abagher2/watch-calc-32/1mm_clearance_button.png

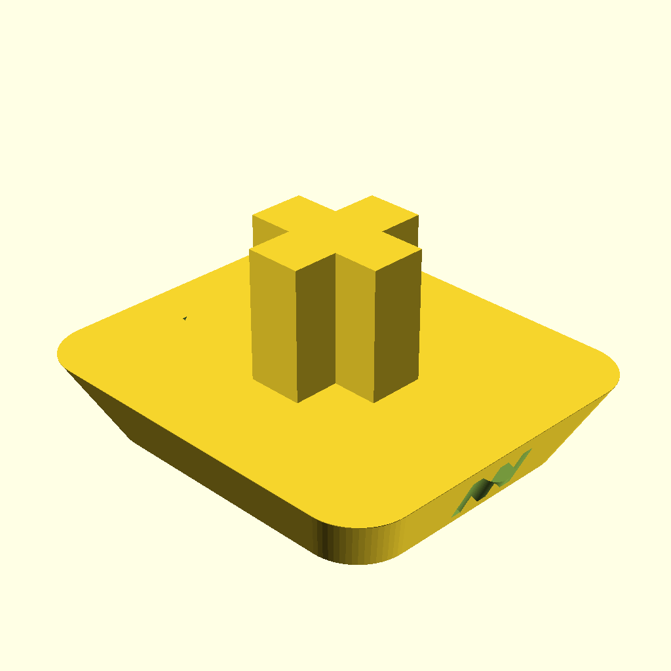
1mm_clearance_button.png
