abagher2/watch-calc-32/bridging_button.png

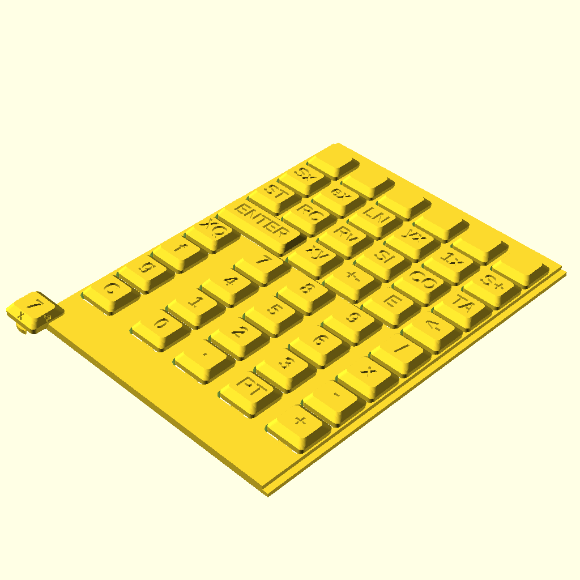
bridging_button.png
