abagher2/watch-calc-32/button_faceplate_captive.png

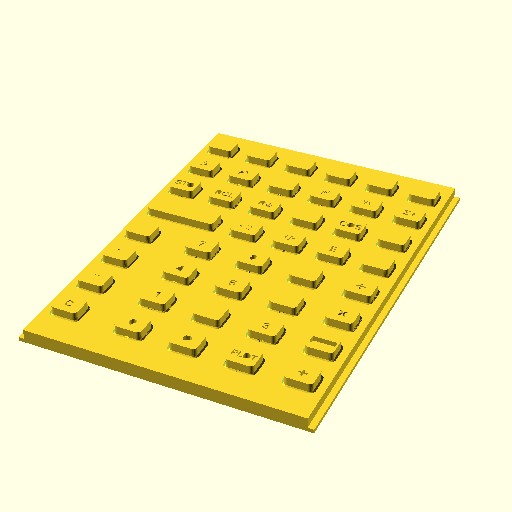
button_faceplate_captive.png
