abagher2/watch-calc-32/button_faceplate_captive_bottom.png

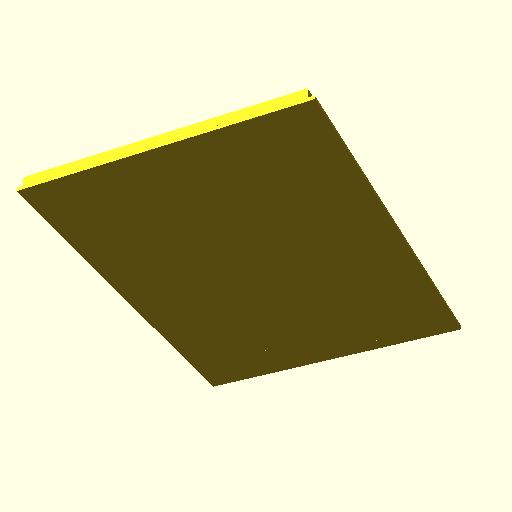
button_faceplate_captive_bottom.png
