abagher2/watch-calc-32/button_faceplate_fixed.png

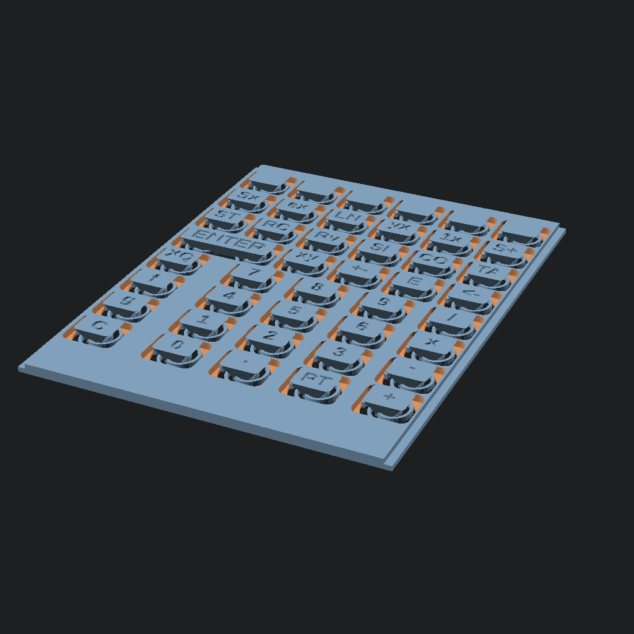
button_faceplate_fixed.png
