abagher2/watch-calc-32/button_faceplate_render4.png

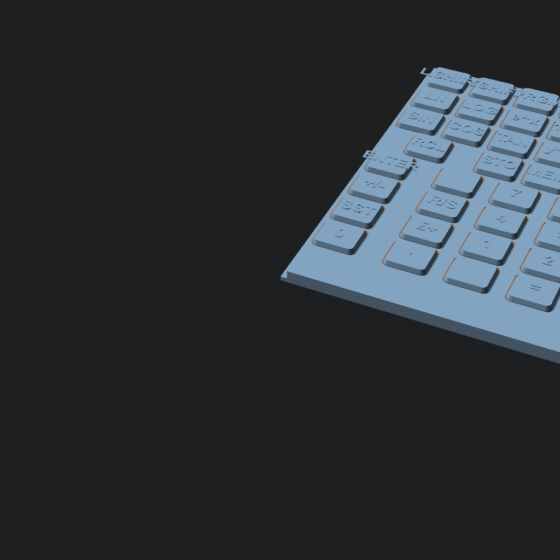
button_faceplate_render4.png
