abagher2/watch-calc-32/chiclet_emojis_updated.png

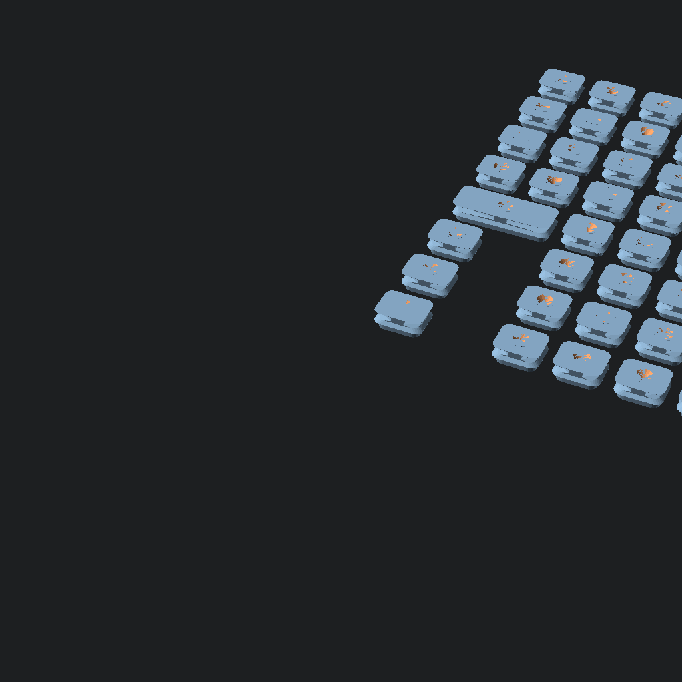
chiclet_emojis_updated.png
