abagher2/watch-calc-32/fastlane/screenshots_raw/en-US/iPad Pro 13-inch (M5)-1-Main.png

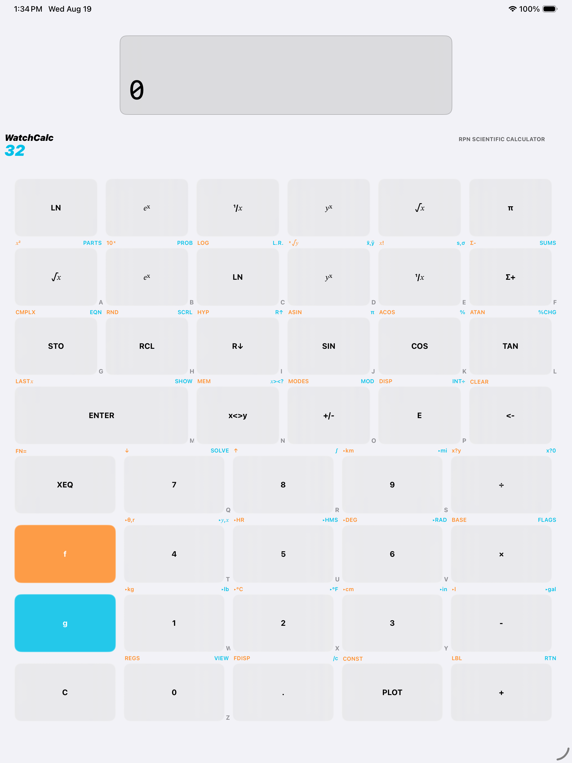
fastlane/screenshots_raw/en-US/iPad Pro 13-inch (M5)-1-Main.png
