abagher2/watch-calc-32/fastlane/screenshots_raw/en-US/iPad Pro 13-inch (M5)-2-Equation.png

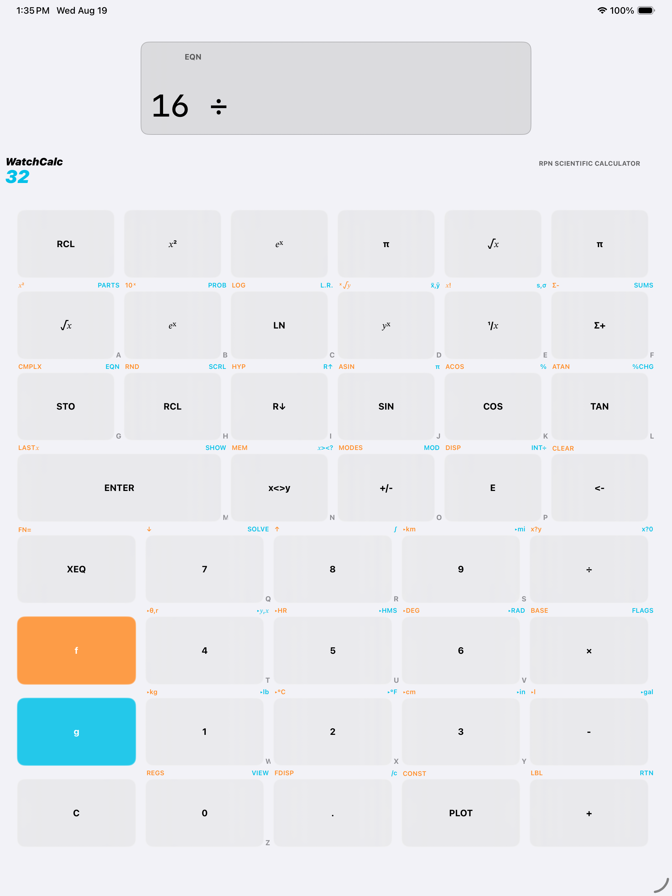
fastlane/screenshots_raw/en-US/iPad Pro 13-inch (M5)-2-Equation.png
