abagher2/watch-calc-32/fastlane/screenshots_raw/en-US/iPad Pro 13-inch (M5)-3-Plot.png

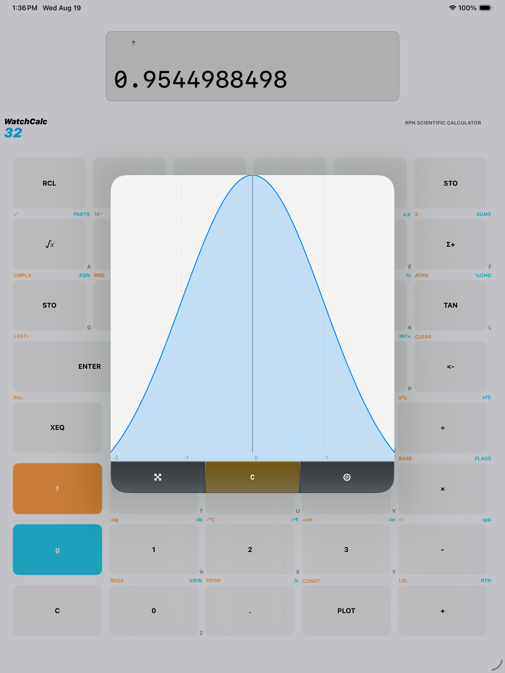
fastlane/screenshots_raw/en-US/iPad Pro 13-inch (M5)-3-Plot.png
