abagher2/watch-calc-32/Hardware/button_faceplate_captive_bottom.png

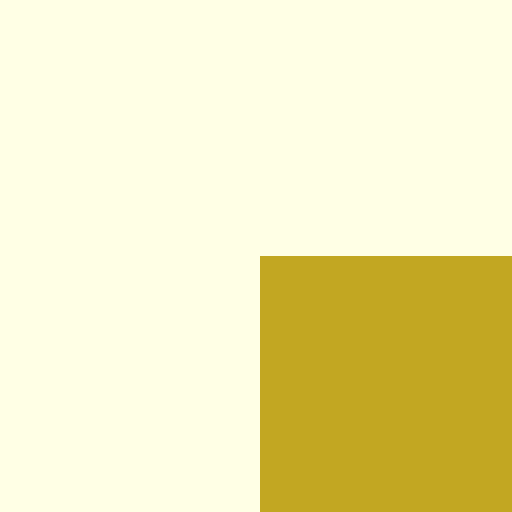
Hardware/button_faceplate_captive_bottom.png
