abagher2/watch-calc-32/Hardware/button_faceplate_first_layer.png

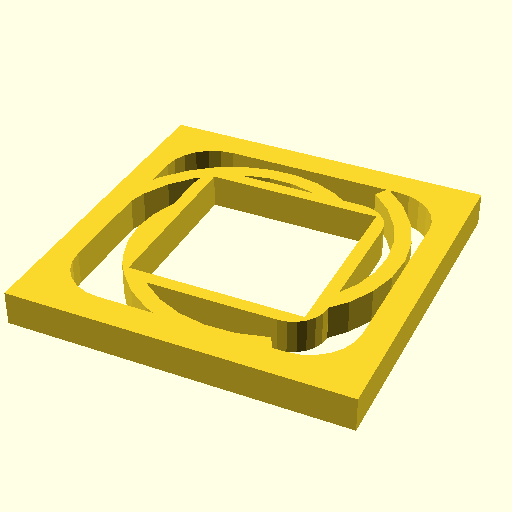
Hardware/button_faceplate_first_layer.png
