abagher2/watch-calc-32/Hardware/button_faceplate_hybrid_top.png

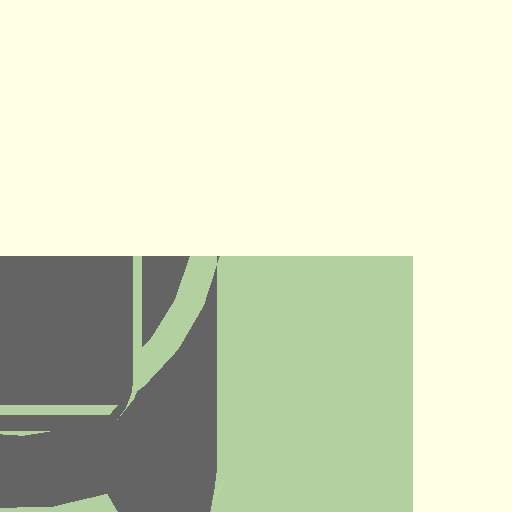
Hardware/button_faceplate_hybrid_top.png
