abagher2/watch-calc-32/Hardware/button_faceplate_lattice.png

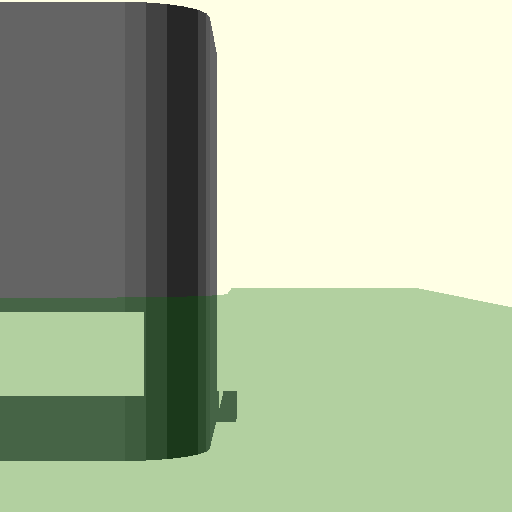
Hardware/button_faceplate_lattice.png
