abagher2/watch-calc-32/Hardware/button_faceplate_modular.png

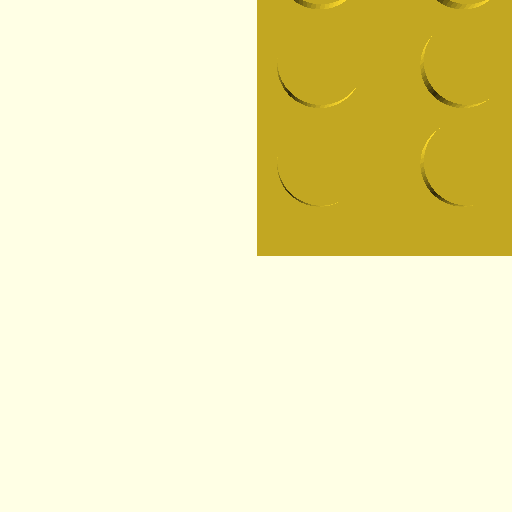
Hardware/button_faceplate_modular.png
