abagher2/watch-calc-32/Hardware/button_faceplate_pocket.png

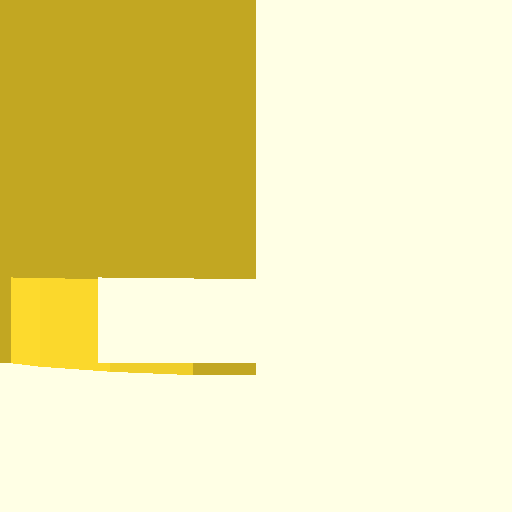
Hardware/button_faceplate_pocket.png
