abagher2/watch-calc-32/Hardware/button_faceplate_section.png

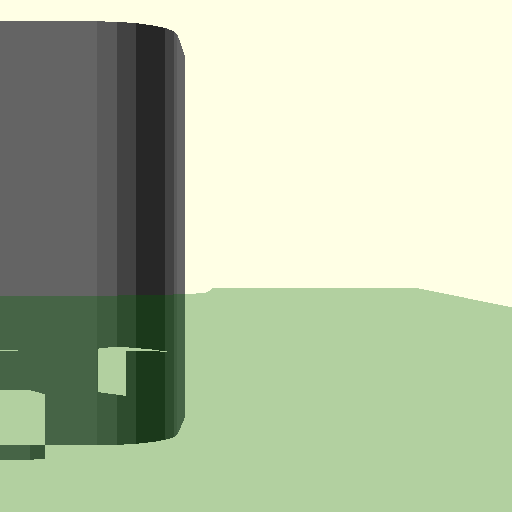
Hardware/button_faceplate_section.png
