abagher2/watch-calc-32/Hardware/button_faceplate_single.png

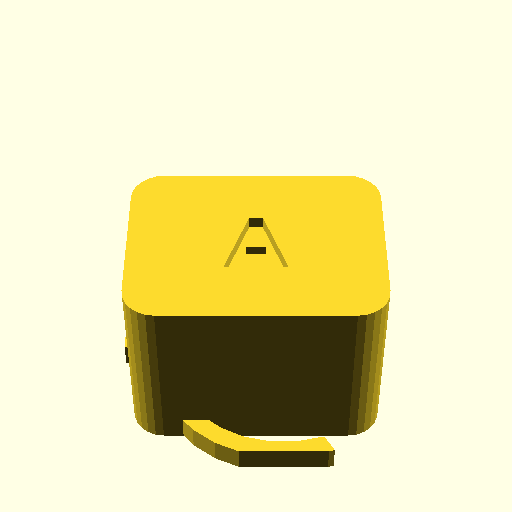
Hardware/button_faceplate_single.png
