abagher2/watch-calc-32/Hardware/button_v9_360_top.png

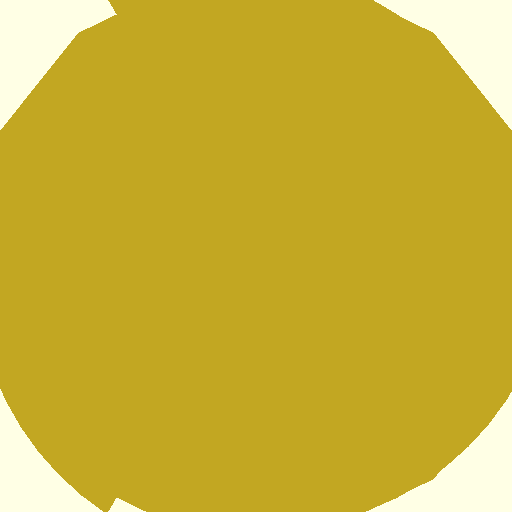
Hardware/button_v9_360_top.png
