abagher2/watch-calc-32/Hardware/button_v9_coils3.png

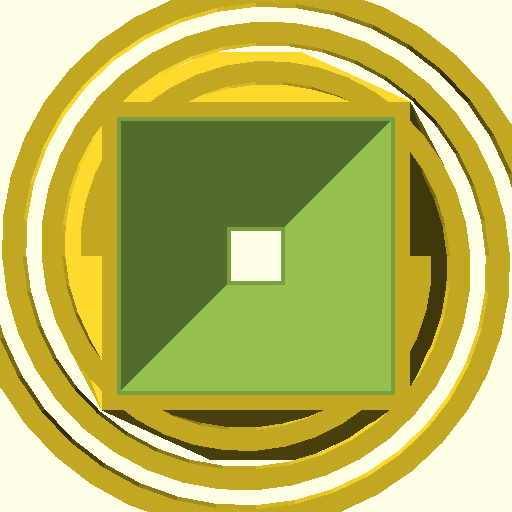
Hardware/button_v9_coils3.png
