abagher2/watch-calc-32/Hardware/button_v9_coils_bottom.png

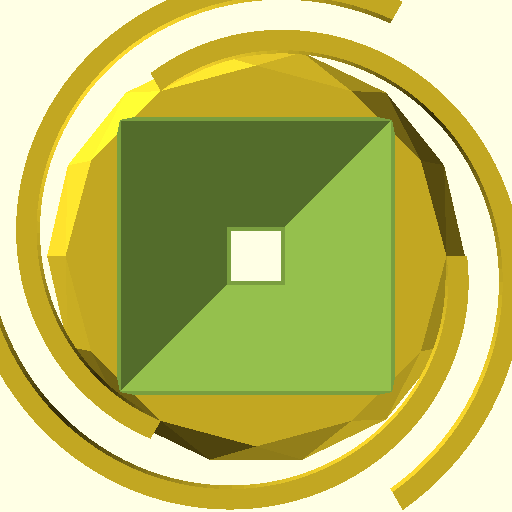
Hardware/button_v9_coils_bottom.png
