abagher2/watch-calc-32/Hardware/chassis_bottom.png

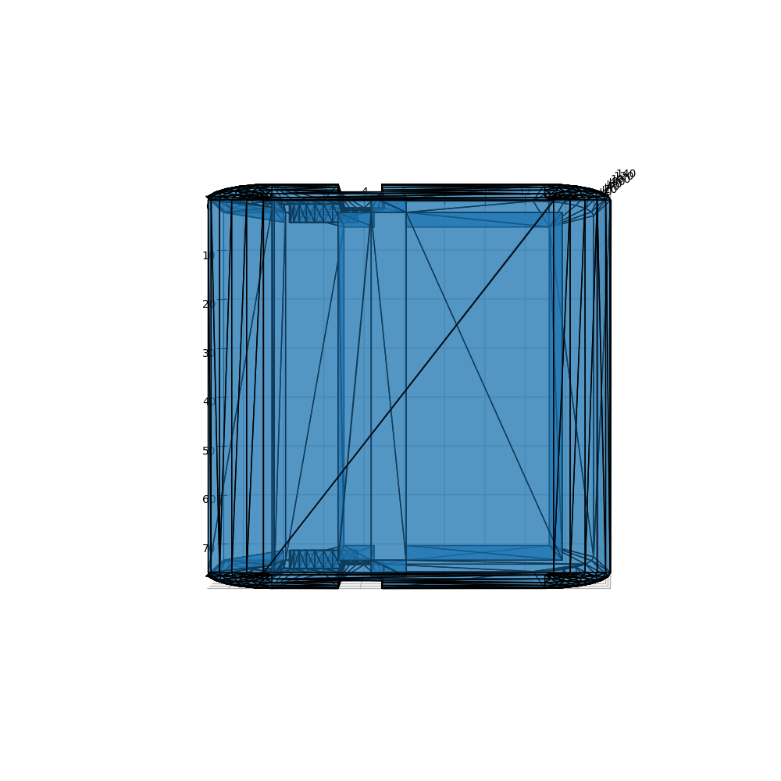
Hardware/chassis_bottom.png
