abagher2/watch-calc-32/Hardware/chassis_front.png

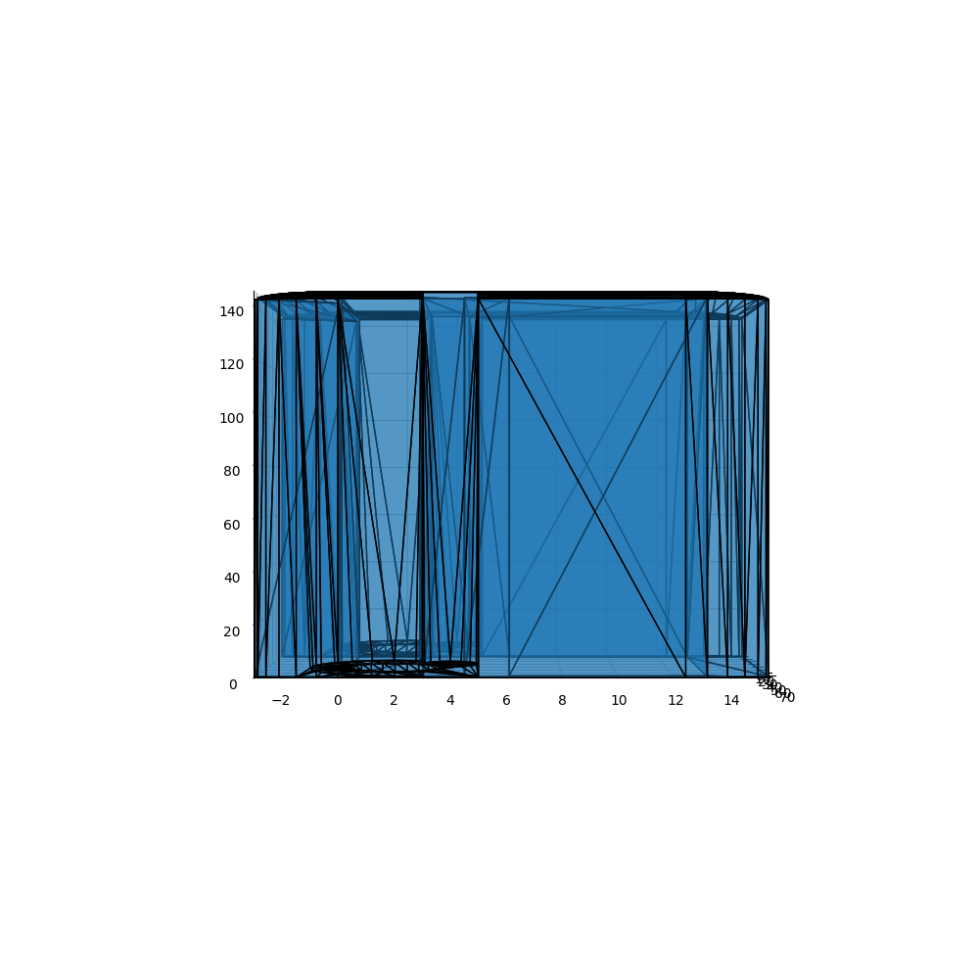
Hardware/chassis_front.png
