abagher2/watch-calc-32/Hardware/chiclet_sf_bottom2.png

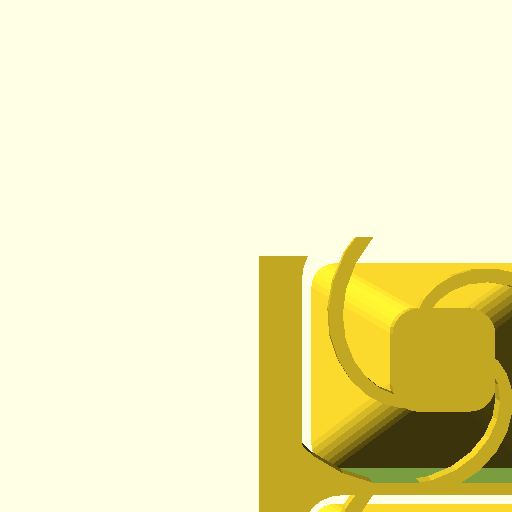
Hardware/chiclet_sf_bottom2.png
