abagher2/watch-calc-32/Hardware/designs/designs/HP_32SII.jpg

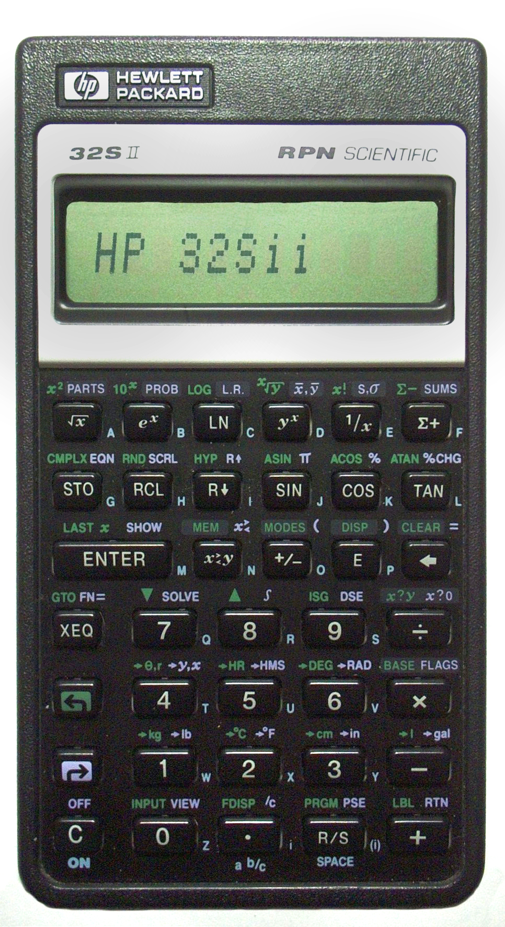
Hardware/designs/designs/HP_32SII.jpg
