abagher2/watch-calc-32/Hardware/designs/HP15c-front-300dpi.jpg

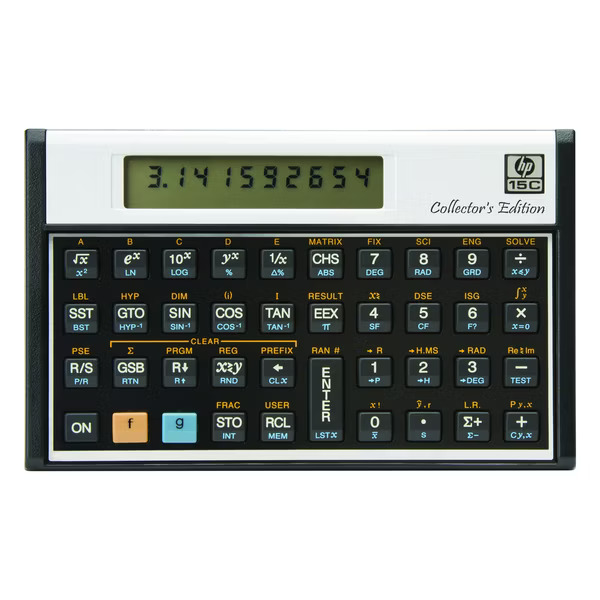
Hardware/designs/HP15c-front-300dpi.jpg
