abagher2/watch-calc-32/Hardware/designs/HP_32SII_blue.jpg

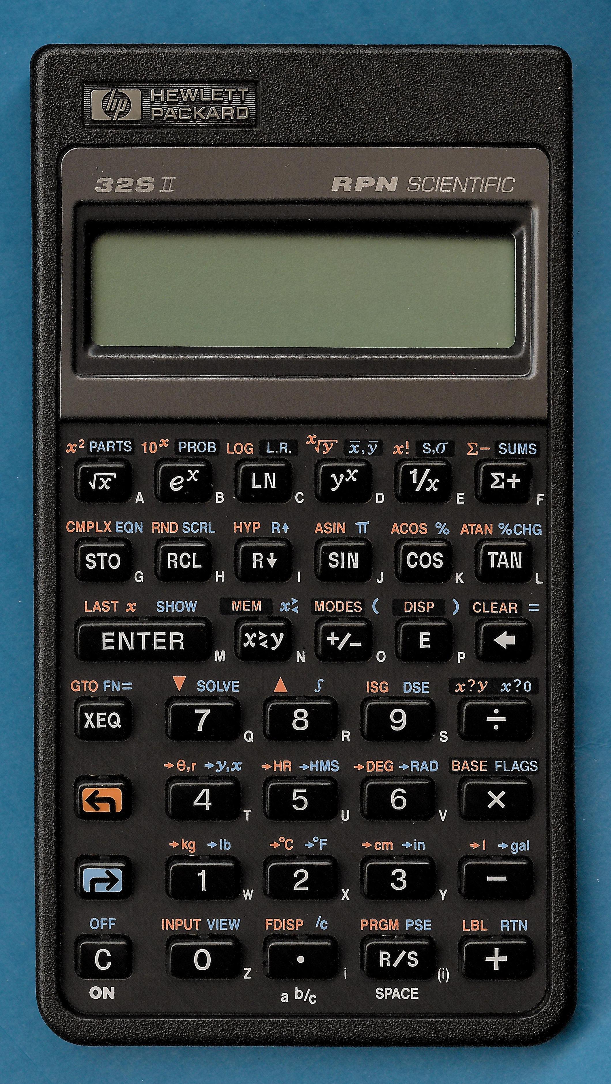
Hardware/designs/HP_32SII_blue.jpg
