abagher2/watch-calc-32/Hardware/designs/Screenshot 2026-08-13 at 9.24.19 AM.png

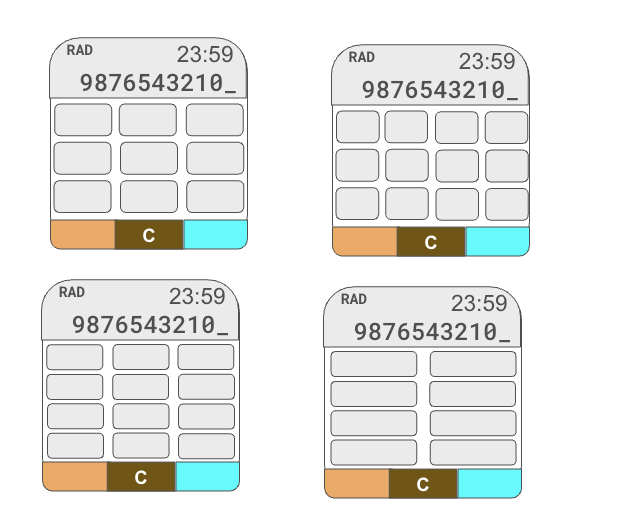
Hardware/designs/Screenshot 2026-08-13 at 9.24.19 AM.png
