abagher2/watch-calc-32/Hardware/final_buttons_bottom.png

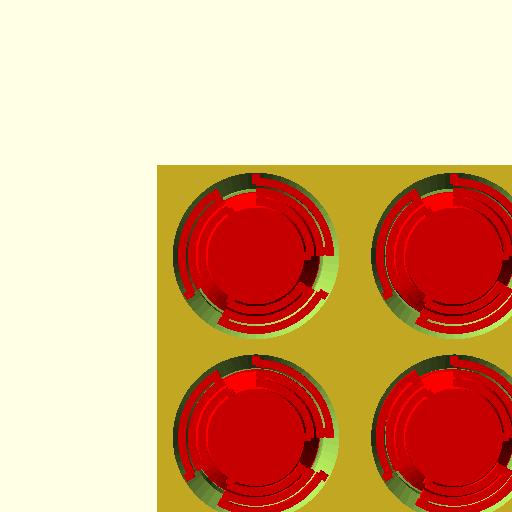
Hardware/final_buttons_bottom.png
