abagher2/watch-calc-32/Hardware/final_buttons_top_labels.png

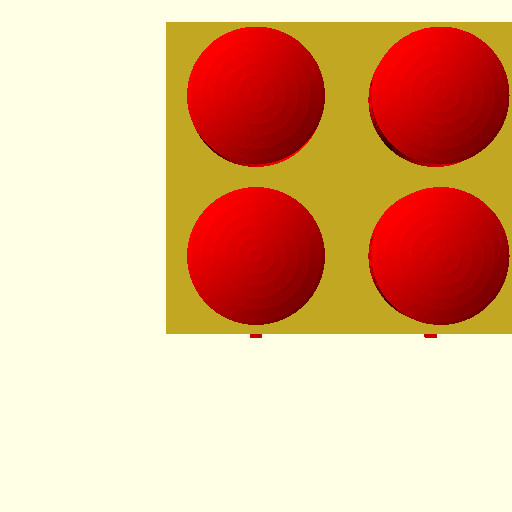
Hardware/final_buttons_top_labels.png
