abagher2/watch-calc-32/Hardware/uv_silkscreen_preview.png

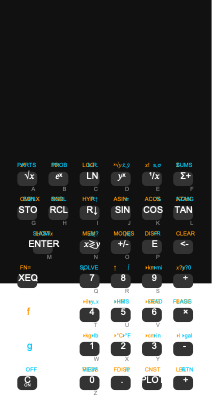
Hardware/uv_silkscreen_preview.png
