abagher2/watch-calc-32/inverted_pyramid.png

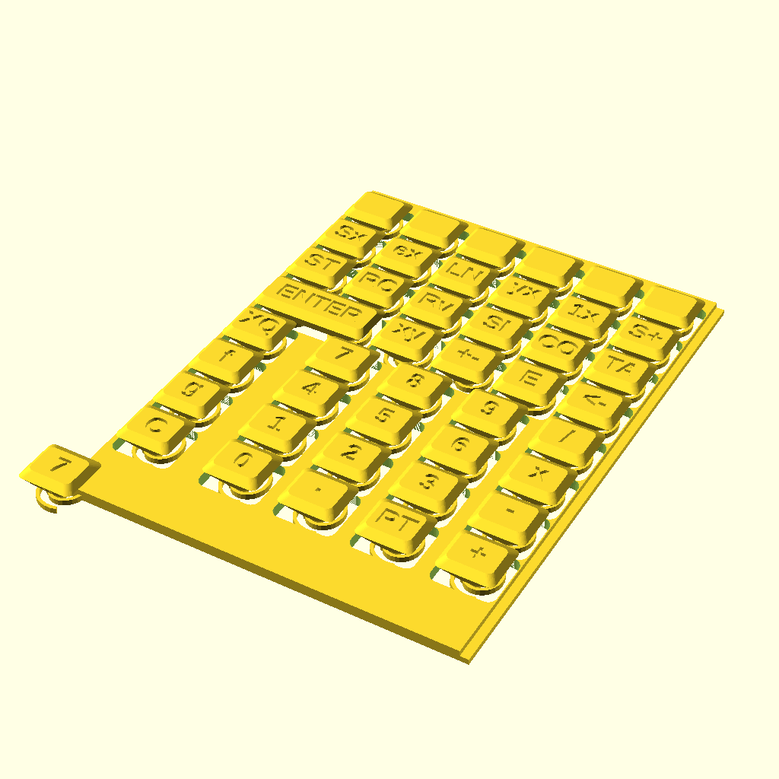
inverted_pyramid.png
