abagher2/watch-calc-32/parity_multiline_1_ios_rendered.png

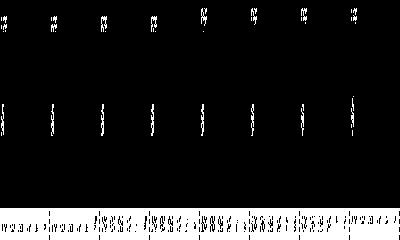
parity_multiline_1_ios_rendered.png
