abagher2/watch-calc-32/top_view.png

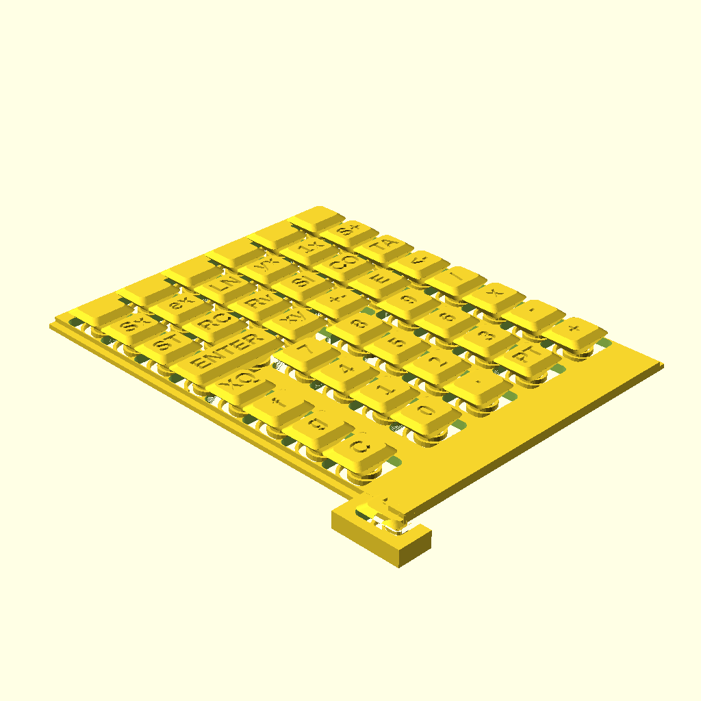
top_view.png
