abagher2/watch-calc-32/Hardware/coil_test2.png

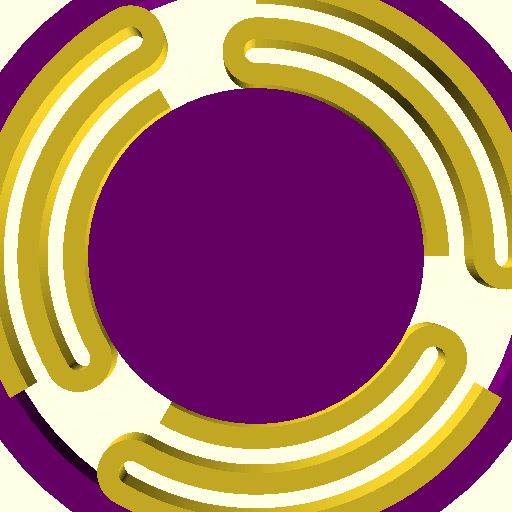
Hardware/coil_test2.png
