abagher2/watch-calc-32/Hardware/coil_test5.png

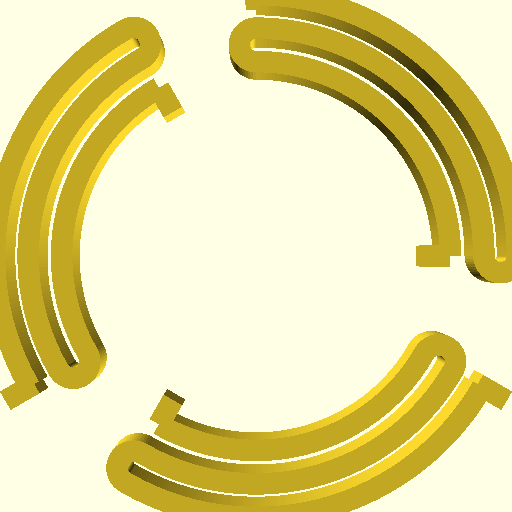
Hardware/coil_test5.png
