abagher2/watch-calc-32/Hardware/coil_test6.png

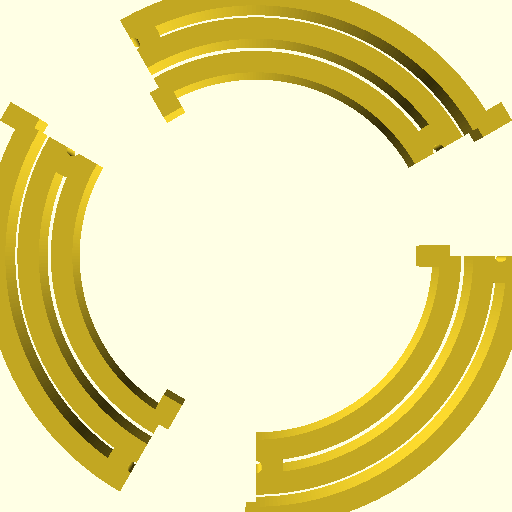
Hardware/coil_test6.png
