abagher2/watch-calc-32/Hardware/coil_test7.png

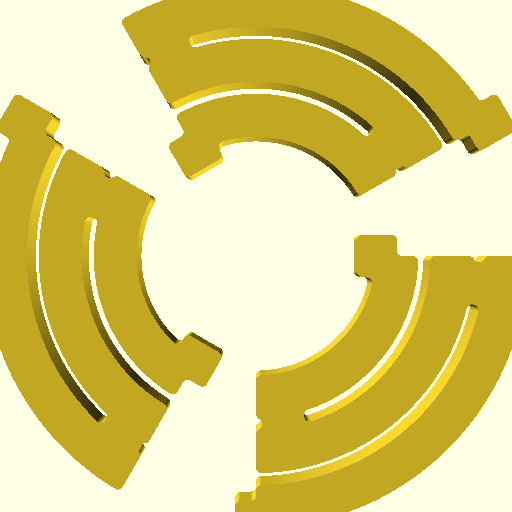
Hardware/coil_test7.png
