abagher2/watch-calc-32/Hardware/coil_test.png

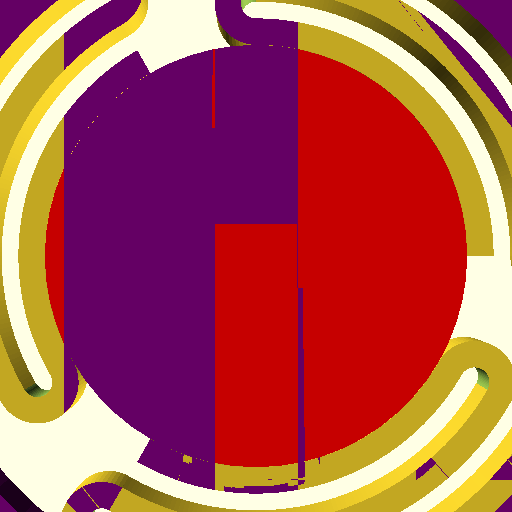
Hardware/coil_test.png
