abagher2/watch-calc-32/Hardware/designs/designs/test_faceplate.jpg

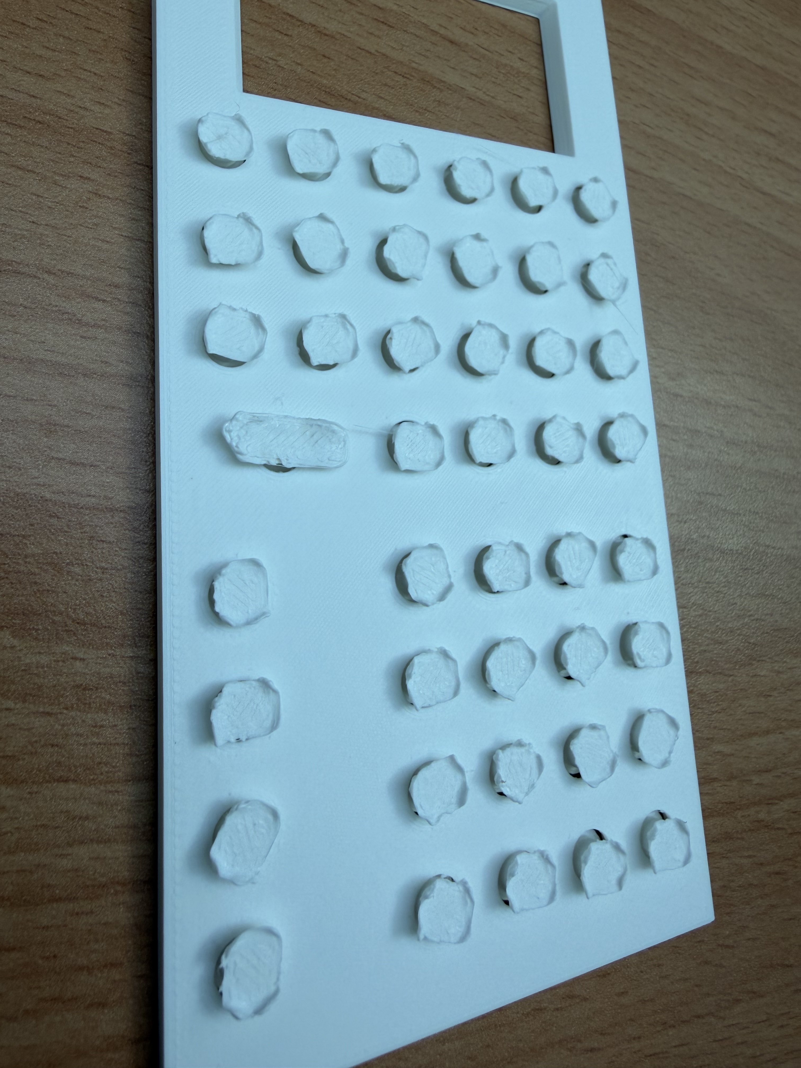
Hardware/designs/designs/test_faceplate.jpg
