abagher2/watch-calc-32/Hardware/final_test_4_buttons.png

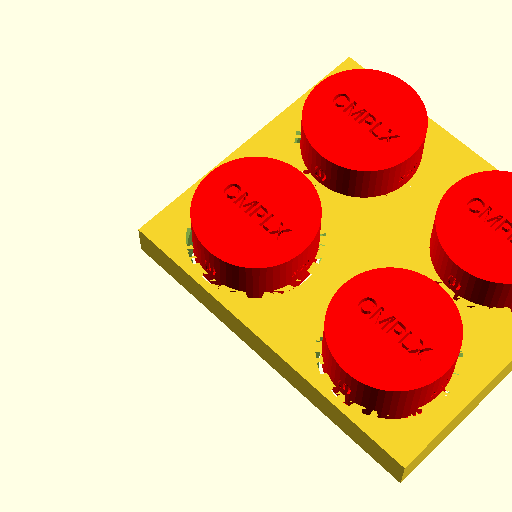
Hardware/final_test_4_buttons.png
