abagher2/watch-calc-32/Hardware/final_test_4_buttons_bottom.png

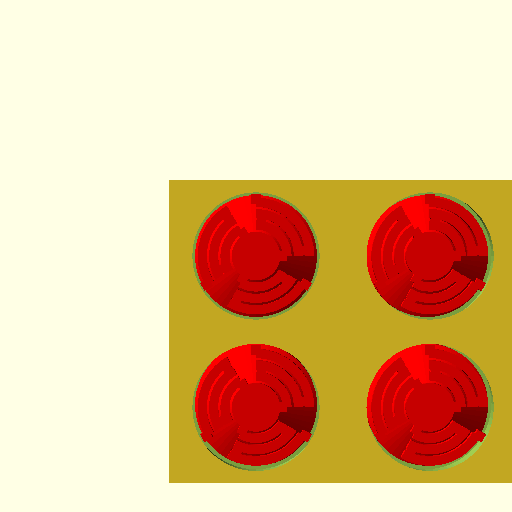
Hardware/final_test_4_buttons_bottom.png
