abagher2/watch-calc-32/Hardware/test_labeled_render.png

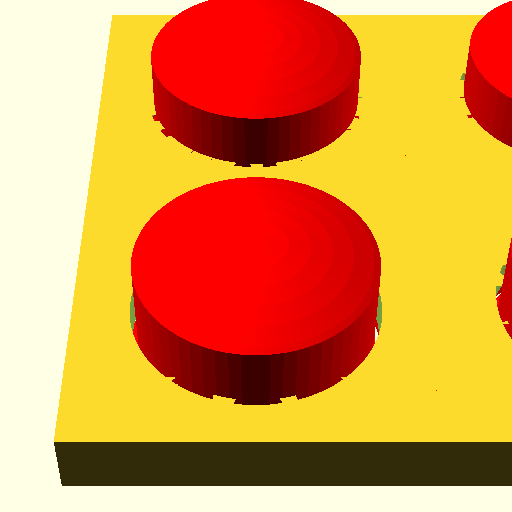
Hardware/test_labeled_render.png
