abagher2/watch-calc-32/Hardware/dump_caps_gen.py

import re
with open("Hardware/generate_scad.py", "r") as f:
    lines = f.readlines()
    for i, line in enumerate(lines):
        if "color(\"Sienna\")" in line:
            print("".join(lines[i-2:i+10]))
            break
