abagher2/watch-calc-32/Hardware/fix_braces.py

with open("generate_scad.py", "r") as f:
    orig = f.read()

# I need to fix the key_button and button_pocket braces, AND chassis_tapered hull, AND tpu_stretch_cover!
# Actually, I can just re-run safe_replace.py after fixing the strings in safe_replace.py, but wait!
# safe_replace.py ALREADY modified generate_scad.py! So I need to restore it from git again first.
